jpsecher/keyboards/pork-chop/kicad/pork-chop-control.kicad_sch

## KiCad design pork-chop/kicad/pork-chop-control.kicad_sch (2022-12-11)

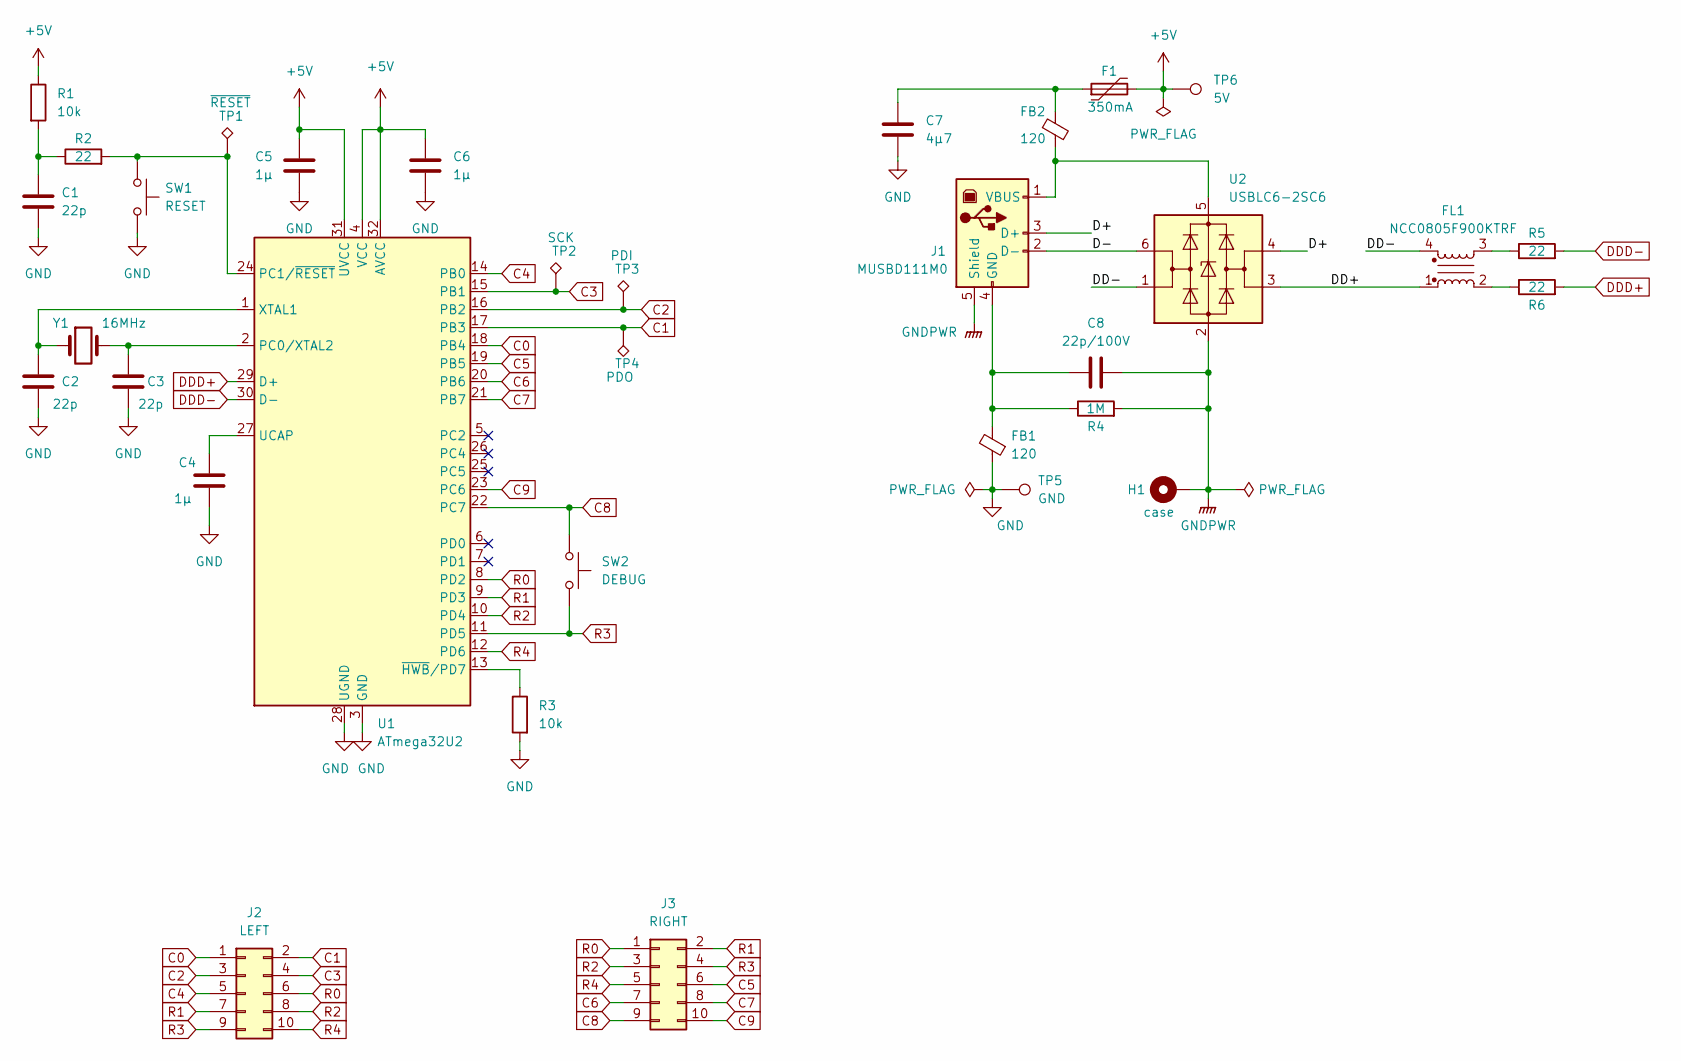
[picture p24: schematic pork-chop-control.kicad_sch]

Parts:
C1, C2, C3: 22p; C_0805_2012Metric_Pad1.18x1.45mm_HandSolder
C4: 1µ; C_1206_3216Metric_Pad1.33x1.80mm_HandSolder
C5, C6: 1µ; C_0805_2012Metric_Pad1.18x1.45mm_HandSolder
C7: 4µ7; C_0805_2012Metric_Pad1.18x1.45mm_HandSolder
C8: 22p/100V; C_0805_2012Metric_Pad1.18x1.45mm_HandSolder
F1: 350mA; R_1210_3225Metric_Pad1.30x2.65mm_HandSolder
FB1, FB2: 120; R_0805_2012Metric_Pad1.20x1.40mm_HandSolder
FL1: NCC0805F900KTRF; L_CommonModeChoke_Coilcraft_0805USB
H1: case; MountingHole_3.2mm_M3_DIN965_Pad
J1: MUSBD111M0; AMPHENOL_MUSBD111M0
J2: LEFT; IDC-Header_2x05_P2.54mm_Horizontal
J3: RIGHT; IDC-Header_2x05_P2.54mm_Horizontal
R1, R3: 10k; R_0805_2012Metric_Pad1.20x1.40mm_HandSolder
R2, R5, R6: 22; R_0805_2012Metric_Pad1.20x1.40mm_HandSolder
R4: 1M; R_0805_2012Metric_Pad1.20x1.40mm_HandSolder
SW1: RESET; SW_SPST_EVQQ2
SW2: DEBUG; SW_SPST_EVQQ2
TP1: ~{RESET}; TestPoint_Pad_1.0x1.0mm
TP2: SCK; TestPoint_Pad_1.0x1.0mm
TP3: PDI; TestPoint_Pad_1.0x1.0mm
TP4: PDO; TestPoint_Pad_1.0x1.0mm
TP5: GND; TestPoint_Pad_1.0x1.0mm
TP6: 5V; TestPoint_Pad_1.0x1.0mm
U1: ATmega32U2; TQFP-32_7x7mm_P0.8mm
U2: USBLC6-2SC6; SOT-23-6
Y1: 16MHz; Crystal_SMD_HC49-SD

Connections:
+5V: C5.1, C6.1, F1.2, R1.1, TP6.1, U1.4 (VCC), U1.31 (UVCC), U1.32 (AVCC)
C0: J2.1, U1.18 (PB4)
C1: J2.2, TP4.1, U1.17 (PB3)
C2: J2.3, TP3.1, U1.16 (PB2)
C3: J2.4, TP2.1, U1.15 (PB1)
C4: J2.5, U1.14 (PB0)
C5: J3.6, U1.19 (PB5)
C6: J3.7, U1.20 (PB6)
C7: J3.8, U1.21 (PB7)
C8: J3.9, SW2.1, U1.22 (PC7)
C9: J3.10, U1.23 (PC6)
D+: J1.3 (D+), U2.4 (I/O2)
D-: J1.2 (D-), U2.6 (I/O1)
DD+: FL1.1, U2.3 (I/O2)
DD-: FL1.4, U2.1 (I/O1)
DDD+: R6.2, U1.29 (D+)
DDD-: R5.2, U1.30 (D-)
GND: C1.2, C2.2, C3.2, C4.2, C5.2, C6.2, C7.2, FB1.1, R3.2, SW1.2, TP5.1, U1.3 (GND), U1.28 (UGND)
GNDPWR: C8.1, H1.1, J1.5 (Shield), R4.2, U2.2 (GND)
unnamed: C1.1, R1.2, R2.1
unnamed: C2.1, U1.1 (XTAL1), Y1.1
unnamed: C3.1, U1.2 (PC0/XTAL2), Y1.2
unnamed: C4.1, U1.27 (UCAP)
unnamed: C7.1, F1.1, FB2.1
unnamed: C8.2, FB1.2, J1.4 (GND), R4.1
unnamed: FB2.2, J1.1 (VBUS), U2.5 (VBUS)
unnamed: FL1.2, R6.1
unnamed: FL1.3, R5.1
unnamed: R2.2, SW1.1, TP1.1, U1.24 (PC1/~RESET)
unnamed: R3.1, U1.13 (~HWB/PD7)
R0: J2.6, J3.1, U1.8 (PD2)
R1: J2.7, J3.2, U1.9 (PD3)
R2: J2.8, J3.3, U1.10 (PD4)
R3: J2.9, J3.4, SW2.2, U1.11 (PD5)
R4: J2.10, J3.5, U1.12 (PD6)
