jpsecher/keyboards/pork-chop/kicad/pork-chop.kicad_sch

## KiCad design pork-chop/kicad/pork-chop.kicad_sch (2022-12-18)

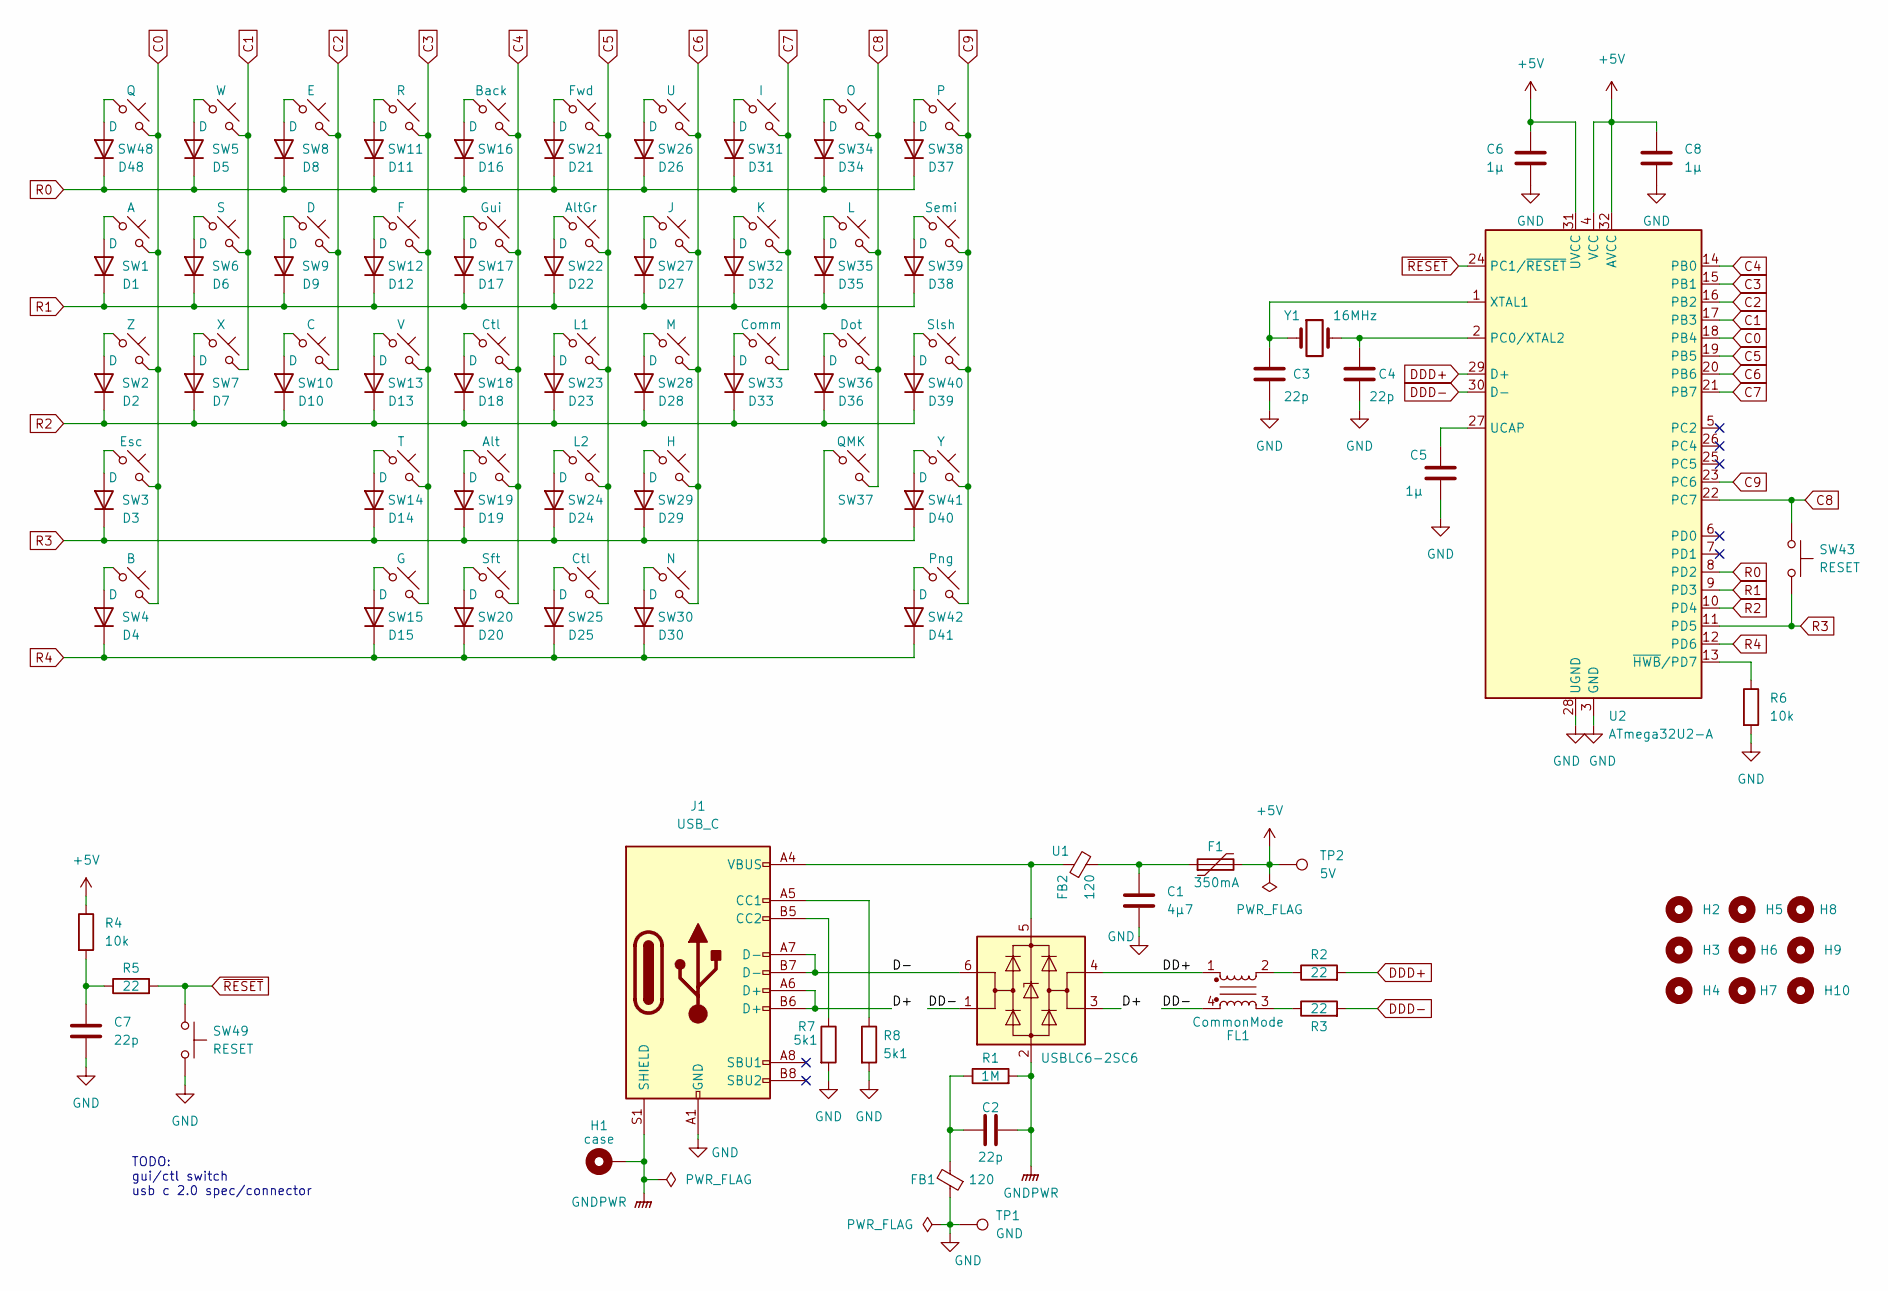
[picture p25: schematic pork-chop.kicad_sch]

Parts:
C1: 4µ7
C2, C3, C4, C7: 22p
C5, C6, C8: 1µ
D1, D2, D3, D4, D5, D6, D7, D8, D9, D10, D11, D12, D13, D14, D15, D16, D17, D18, D19, D20, D21, D22, D23, D24, D25, D26, D27, D28, D29, D30, D31, D32, D33, D34, D35, D36, D37, D38, D39, D40, D41, D48: D
F1: 350mA
FB1, FB2: 120
FL1: CommonMode
H1: case; MountingHole_3.2mm_M3_ISO14580_Pad
H2, H3, H4, H5, H6, H7, H8, H9, H10: MountingHole; MountingHole_3.2mm_M3
J1: USB_C
R1: 1M
R2, R3, R5: 22
R4, R6: 10k
R7, R8: 5k1
SW1: A
SW2: Z
SW3: Esc
SW4: B
SW5: W
SW6: S
SW7: X
SW8: E
SW9: D
SW10: C
SW11: R
SW12: F
SW13: V
SW14: T
SW15: G
SW16: Back
SW17: Gui
SW18, SW25: Ctl
SW19: Alt
SW20: Sft
SW21: Fwd
SW22: AltGr
SW23: L1
SW24: L2
SW26: U
SW27: J
SW28: M
SW29: H
SW30: N
SW31: I
SW32: K
SW33: Comm
SW34: O
SW35: L
SW36: Dot
SW37: QMK
SW38: P
SW39: Semi
SW40: Slsh
SW41: Y
SW42: Png
SW43, SW49: RESET
SW48: Q
TP1: GND
TP2: 5V
U1: USBLC6-2SC6; SOT-23-6
U2: ATmega32U2-A; TQFP-32_7x7mm_P0.8mm
Y1: 16MHz

Connections:
+5V: C6.1, C8.1, F1.2, R4.1, TP2.1, U2.4 (VCC), U2.31 (UVCC), U2.32 (AVCC)
C0: SW1.2, SW2.2, SW3.2, SW4.2, SW48.2, U2.18 (PB4)
C1: SW5.2, SW6.2, SW7.2, U2.17 (PB3)
C2: SW8.2, SW9.2, SW10.2, U2.16 (PB2)
C3: SW11.2, SW12.2, SW13.2, SW14.2, SW15.2, U2.15 (PB1)
C4: SW16.2, SW17.2, SW18.2, SW19.2, SW20.2, U2.14 (PB0)
C5: SW21.2, SW22.2, SW23.2, SW24.2, SW25.2, U2.19 (PB5)
C6: SW26.2, SW27.2, SW28.2, SW29.2, SW30.2, U2.20 (PB6)
C7: SW31.2, SW32.2, SW33.2, U2.21 (PB7)
C8: SW34.2, SW35.2, SW36.2, SW37.2, SW43.1, U2.22 (PC7)
C9: SW38.2, SW39.2, SW40.2, SW41.2, SW42.2, U2.23 (PC6)
D+: J1.A6 (D+), J1.B6 (D+), U1.3 (I/O2)
D-: J1.A7 (D-), J1.B7 (D-), U1.6 (I/O1)
DD+: FL1.1, U1.4 (I/O2)
DD-: FL1.4, U1.1 (I/O1)
DDD+: R2.2, U2.29 (D+)
DDD-: R3.2, U2.30 (D-)
GND: C1.1, C3.2, C4.2, C5.2, C6.2, C7.2, C8.2, FB1.1, J1.A1 (GND), J1.A12 (GND), J1.B1 (GND), J1.B12 (GND), R6.2, R7.2, R8.2, SW49.2, TP1.1, U2.3 (GND), U2.28 (UGND)
GNDPWR: C2.2, H1.1, J1.S1 (SHIELD), R1.2, U1.2 (GND)
unnamed: C1.2, F1.1, FB2.2
unnamed: C2.1, FB1.2, R1.1
unnamed: C3.1, U2.1 (XTAL1), Y1.1
unnamed: C4.1, U2.2 (PC0/XTAL2), Y1.2
unnamed: C5.1, U2.27 (UCAP)
unnamed: C7.1, R4.2, R5.1
unnamed: D1.2 (A), SW1.1
unnamed: D2.2 (A), SW2.1
unnamed: D3.2 (A), SW3.1
unnamed: D4.2 (A), SW4.1
unnamed: D5.2 (A), SW5.1
unnamed: D6.2 (A), SW6.1
unnamed: D7.2 (A), SW7.1
unnamed: D8.2 (A), SW8.1
unnamed: D9.2 (A), SW9.1
unnamed: D10.2 (A), SW10.1
unnamed: D11.2 (A), SW11.1
unnamed: D12.2 (A), SW12.1
unnamed: D13.2 (A), SW13.1
unnamed: D14.2 (A), SW14.1
unnamed: D15.2 (A), SW15.1
unnamed: D16.2 (A), SW16.1
unnamed: D17.2 (A), SW17.1
unnamed: D18.2 (A), SW18.1
unnamed: D19.2 (A), SW19.1
unnamed: D20.2 (A), SW20.1
unnamed: D21.2 (A), SW21.1
unnamed: D22.2 (A), SW22.1
unnamed: D23.2 (A), SW23.1
unnamed: D24.2 (A), SW24.1
unnamed: D25.2 (A), SW25.1
unnamed: D26.2 (A), SW26.1
unnamed: D27.2 (A), SW27.1
unnamed: D28.2 (A), SW28.1
unnamed: D29.2 (A), SW29.1
unnamed: D30.2 (A), SW30.1
unnamed: D31.2 (A), SW31.1
unnamed: D32.2 (A), SW32.1
unnamed: D33.2 (A), SW33.1
unnamed: D34.2 (A), SW34.1
unnamed: D35.2 (A), SW35.1
unnamed: D36.2 (A), SW36.1
unnamed: D37.2 (A), SW38.1
unnamed: D38.2 (A), SW39.1
unnamed: D39.2 (A), SW40.1
unnamed: D40.2 (A), SW41.1
unnamed: D41.2 (A), SW42.1
unnamed: D48.2 (A), SW48.1
unnamed: FB2.1, J1.A4 (VBUS), J1.A9 (VBUS), J1.B4 (VBUS), J1.B9 (VBUS), U1.5 (VBUS)
unnamed: FL1.2, R2.1
unnamed: FL1.3, R3.1
unnamed: J1.A5 (CC1), R8.1
unnamed: J1.B5 (CC2), R7.1
unnamed: R6.1, U2.13 (~HWB/PD7)
R0: D5.1 (K), D8.1 (K), D11.1 (K), D16.1 (K), D21.1 (K), D26.1 (K), D31.1 (K), D34.1 (K), D37.1 (K), D48.1 (K), U2.8 (PD2)
R1: D1.1 (K), D6.1 (K), D9.1 (K), D12.1 (K), D17.1 (K), D22.1 (K), D27.1 (K), D32.1 (K), D35.1 (K), D38.1 (K), U2.9 (PD3)
R2: D2.1 (K), D7.1 (K), D10.1 (K), D13.1 (K), D18.1 (K), D23.1 (K), D28.1 (K), D33.1 (K), D36.1 (K), D39.1 (K), U2.10 (PD4)
R3: D3.1 (K), D14.1 (K), D19.1 (K), D24.1 (K), D29.1 (K), D40.1 (K), SW37.1, SW43.2, U2.11 (PD5)
R4: D4.1 (K), D15.1 (K), D20.1 (K), D25.1 (K), D30.1 (K), D41.1 (K), U2.12 (PD6)
~RESET: R5.2, SW49.1, U2.24 (PC1/~RESET)

Notes on the sheet:
TODO: gui/ctl switch usb c 2.0 spec/connector
